bandianxuediao/Breastfeeding_clock/DOC/Photos/1.jpg

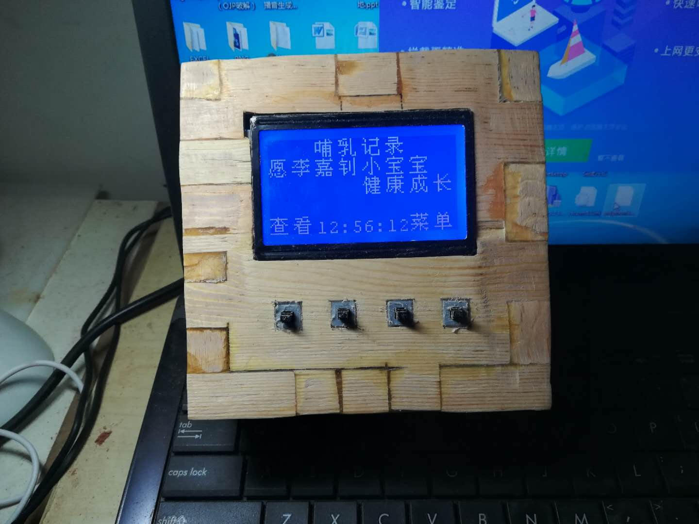
DOC/Photos/1.jpg
