bandianxuediao/Breastfeeding_clock/DOC/Photos/2.jpg

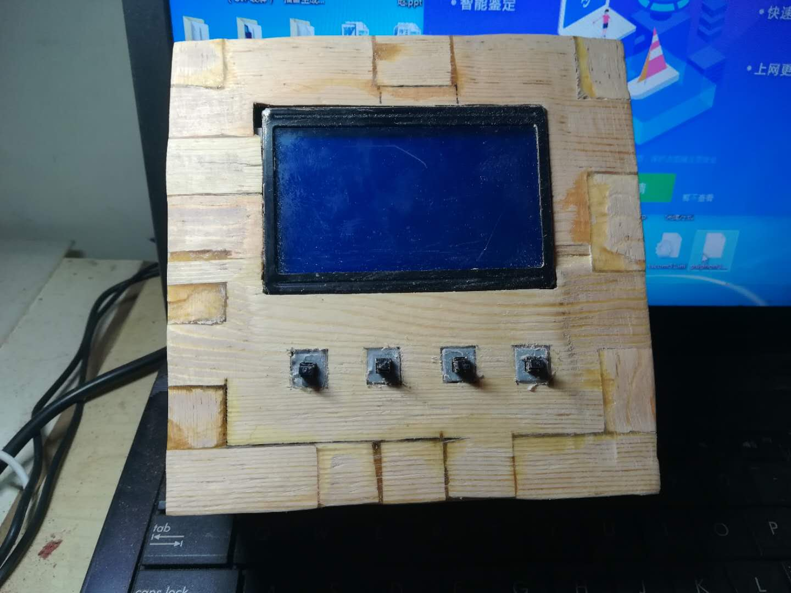
DOC/Photos/2.jpg
