bandianxuediao/Breastfeeding_clock/DOC/Photos/3.jpg

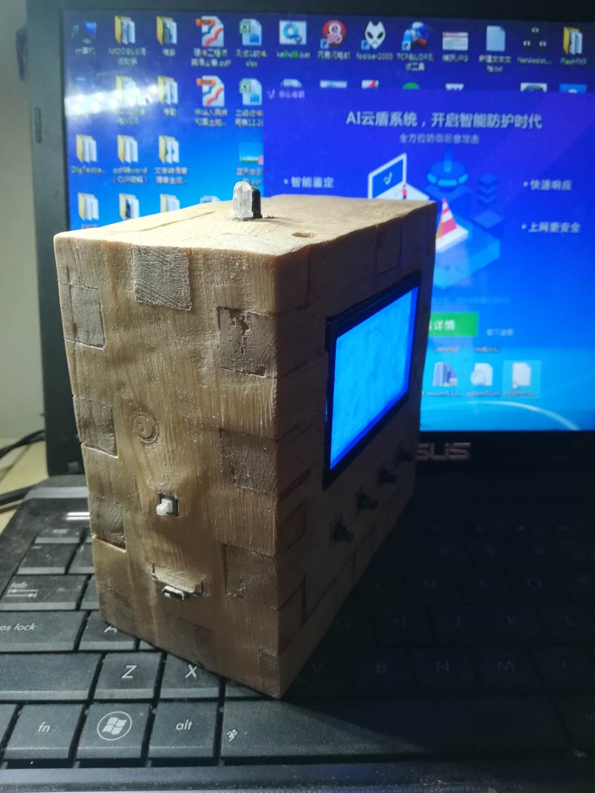
DOC/Photos/3.jpg
