bandianxuediao/Breastfeeding_clock/DOC/Photos/4.jpg

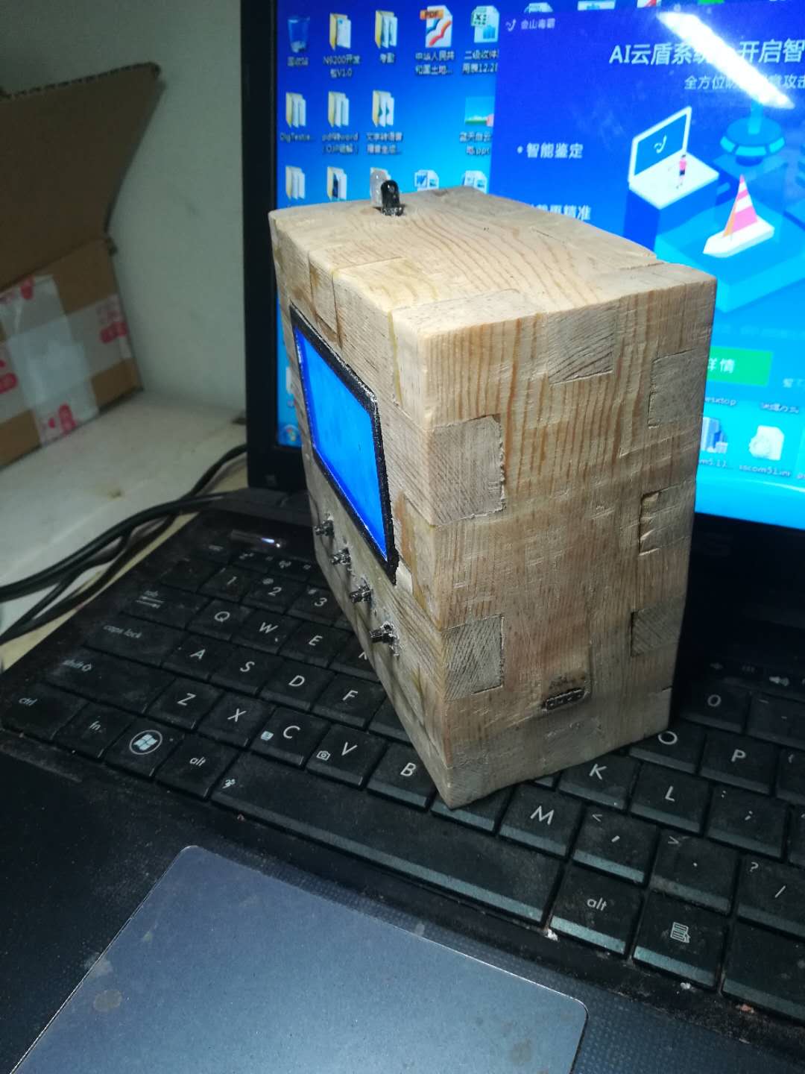
DOC/Photos/4.jpg
