bandianxuediao/Breastfeeding_clock/DOC/Photos/5.jpg

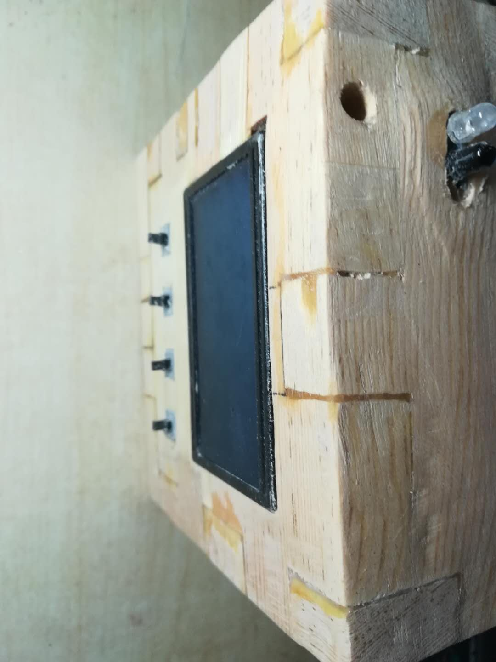
DOC/Photos/5.jpg
