bandianxuediao/Breastfeeding_clock/DOC/Photos/6.jpg

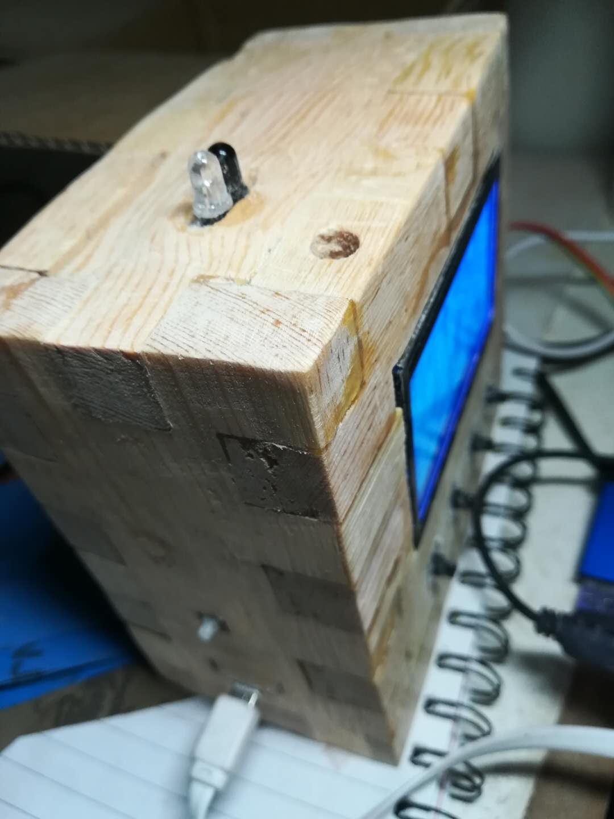
DOC/Photos/6.jpg
