bandianxuediao/Breastfeeding_clock/DOC/Photos/7.jpg

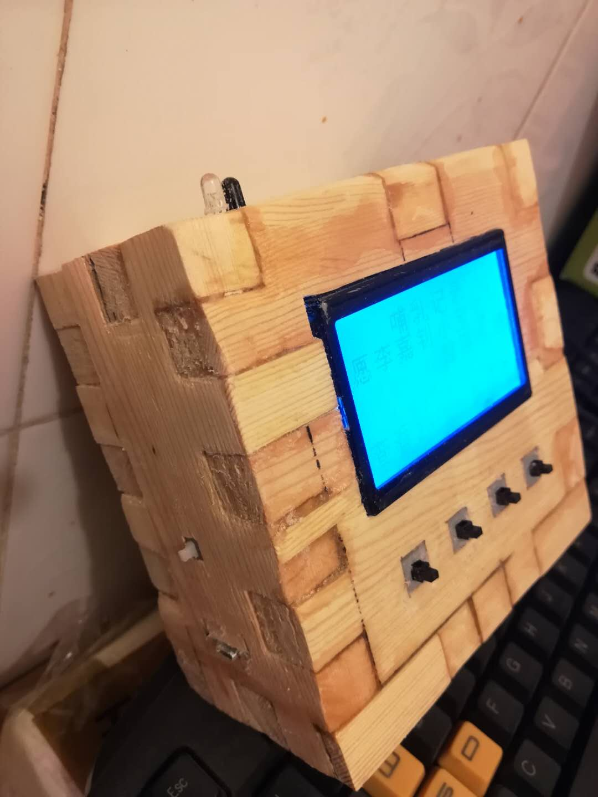
DOC/Photos/7.jpg
