bandianxuediao/Breastfeeding_clock/DOC/Photos/8.jpg

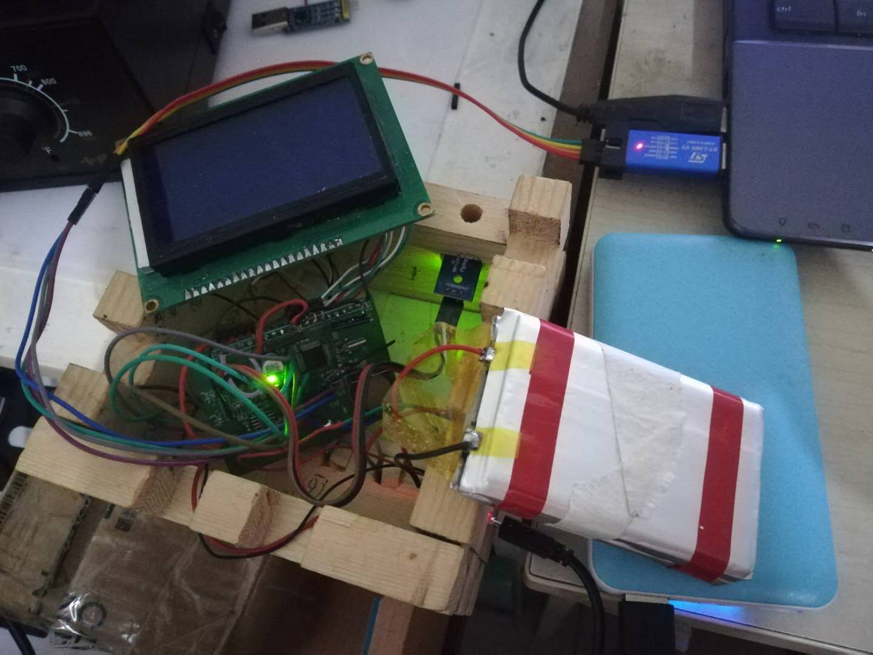
DOC/Photos/8.jpg
