bandianxuediao/Breastfeeding_clock/DOC/Photos/9.jpg

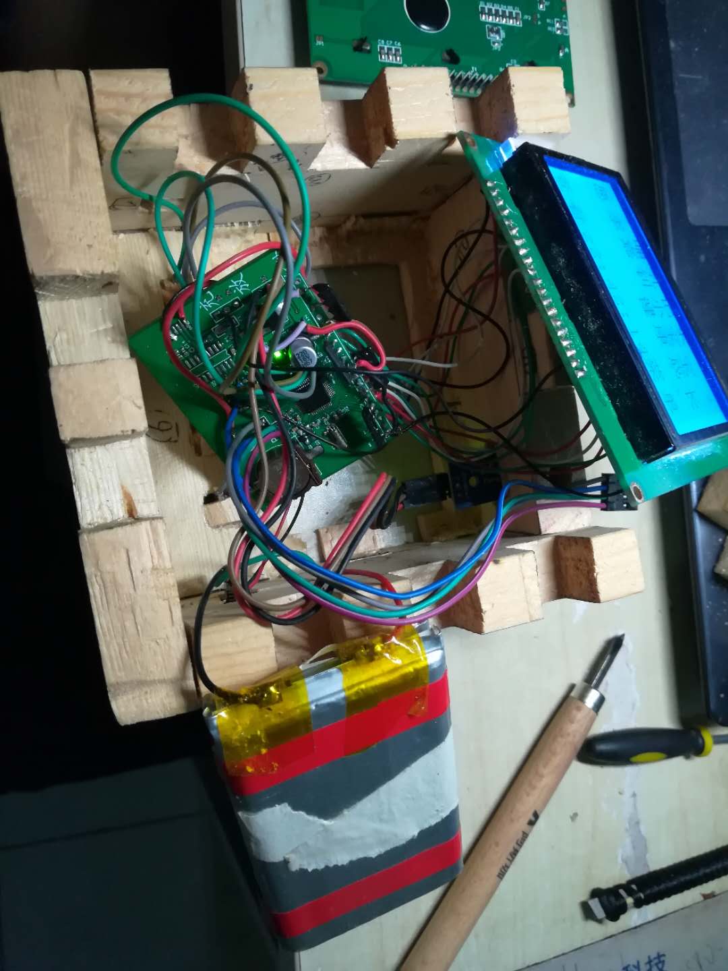
DOC/Photos/9.jpg
