bandianxuediao/Breastfeeding_clock/DOC/Photos/11.jpg

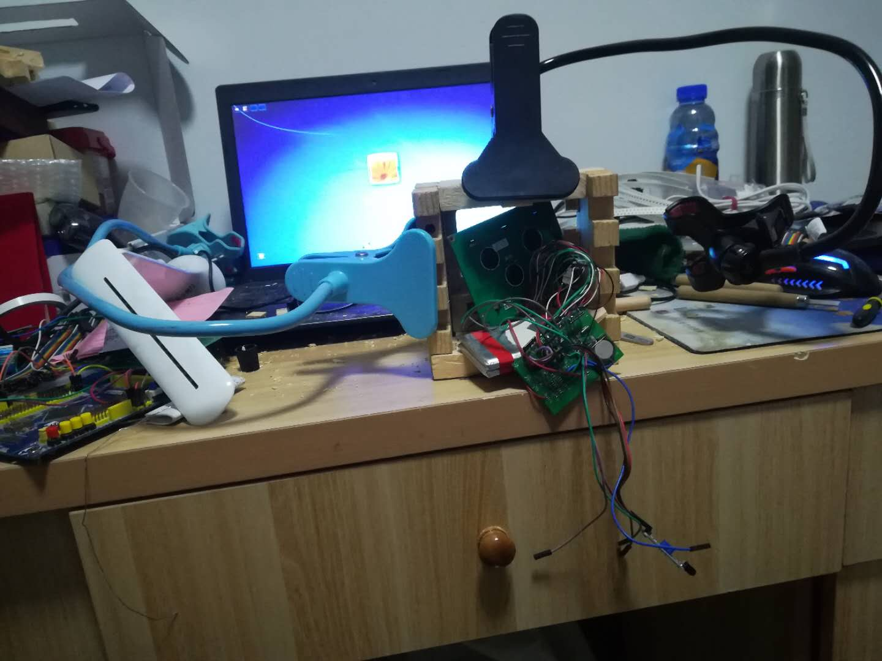
DOC/Photos/11.jpg
