bandianxuediao/Breastfeeding_clock/DOC/Photos/12.jpg

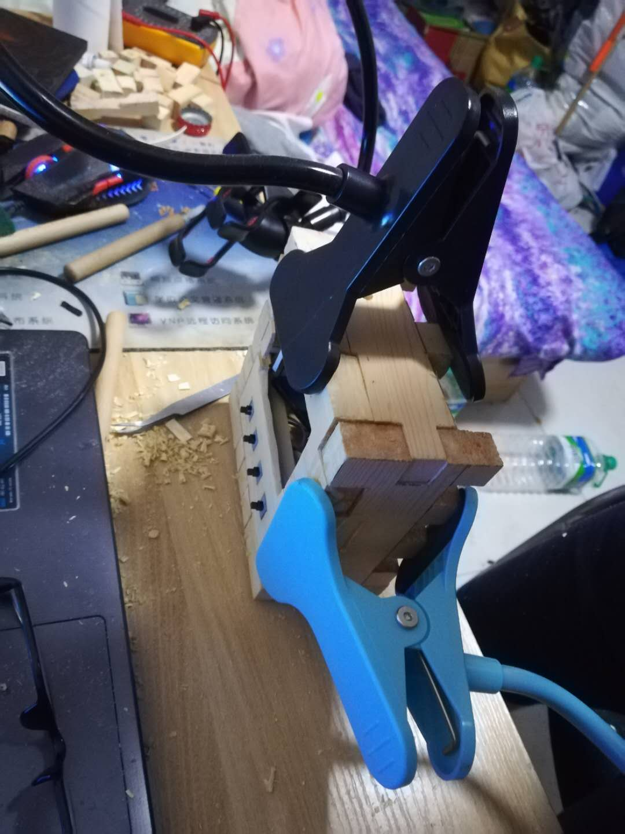
DOC/Photos/12.jpg
