bandianxuediao/Breastfeeding_clock/DOC/Photos/13.jpg

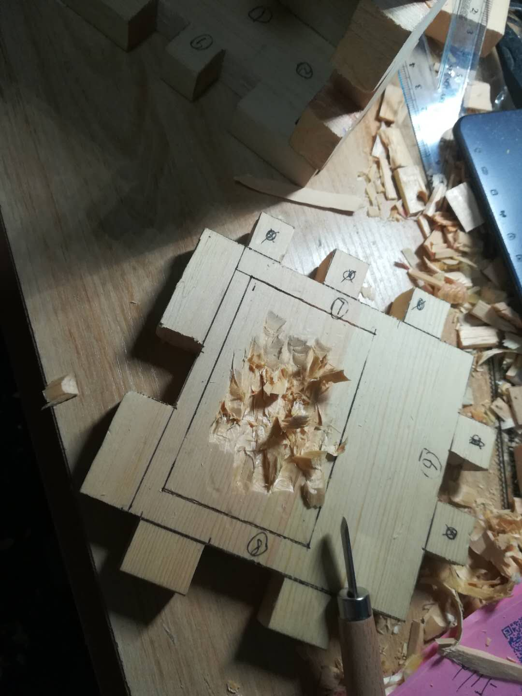
DOC/Photos/13.jpg
