bandianxuediao/Breastfeeding_clock/DOC/Photos/14.jpg

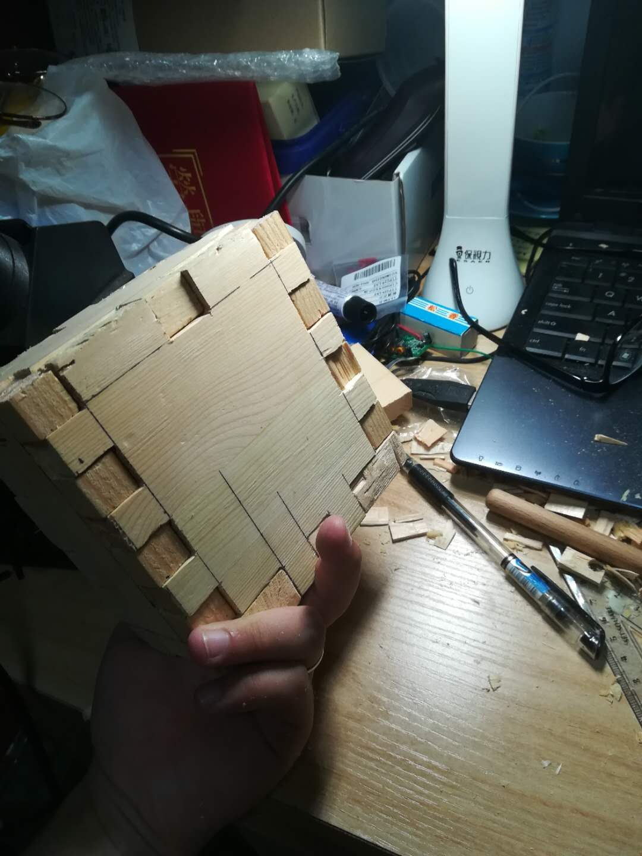
DOC/Photos/14.jpg
