bandianxuediao/Breastfeeding_clock/DOC/Photos/16.jpg

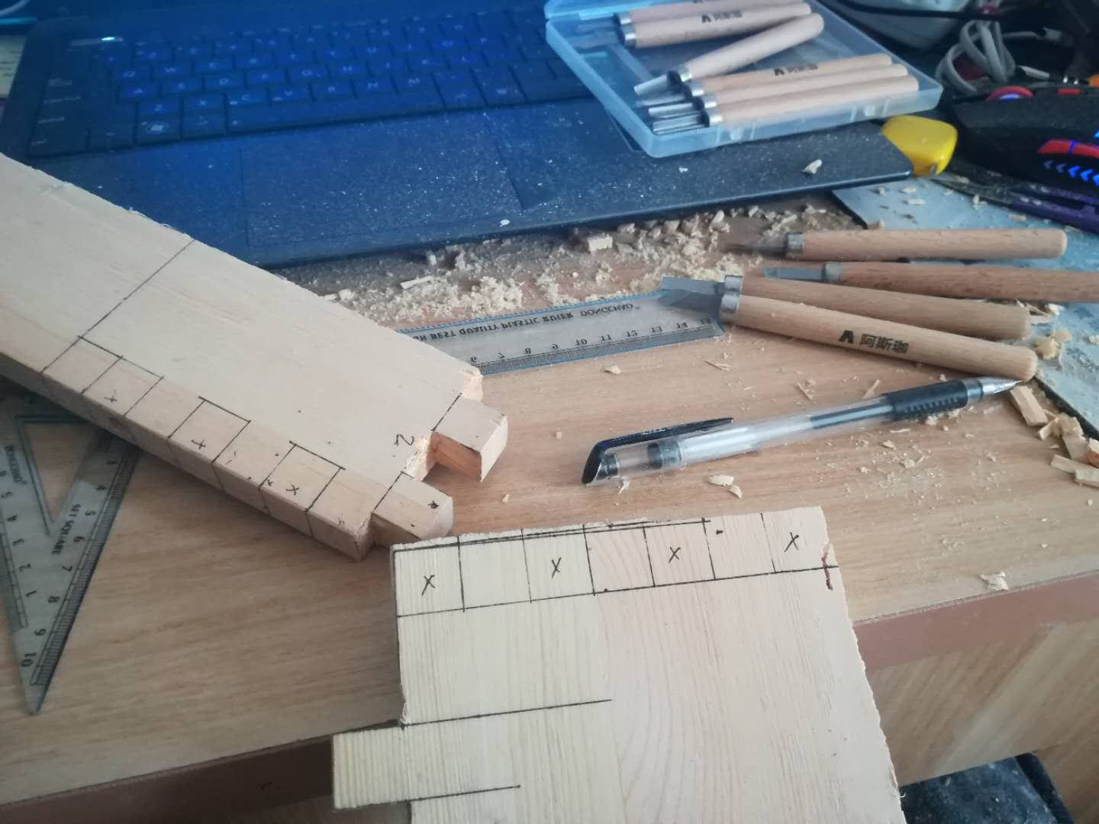
DOC/Photos/16.jpg
