bandianxuediao/Breastfeeding_clock/DOC/Photos/HappyMouse.jpg

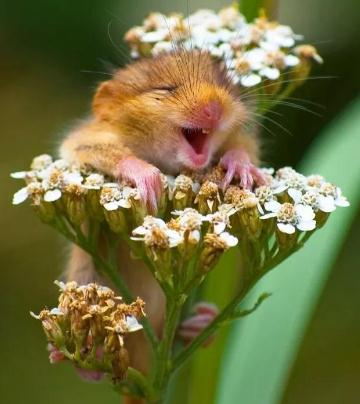
DOC/Photos/HappyMouse.jpg
