bandianxuediao/Breastfeeding_clock/DOC/Photos/soogif.gif

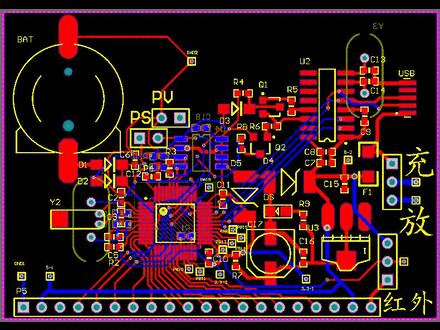
DOC/Photos/soogif.gif
