bandianxuediao/Breastfeeding_clock/Program/HARDWARE/BEEP/beep.h

#ifndef __BEEP_H
#define __BEEP_H
#include "sys.h"
//////////////////////////////////////////////////////////////////////////////////
//本程序只供学习使用，未经作者许可，不得用于其它任何用途

//////////////////////////////////////////////////////////////////////////////////
//蜂鸣器端口定义
#define BEEP PCout(12)  // BEEP,蜂鸣器接口         
#define BL PEout(10)
void BEEP_Init(void);   //初始化

#endif
