bandianxuediao/Breastfeeding_clock/Program/HARDWARE/exti/exti.c

#include "includes.h"


//////////////////////////////////////////////////////////////////////////////////
//本程序只供学习使用，未经作者许可，不得用于其它任何用途
//ALIENTEK精英STM32开发板
//外部中断 驱动代码
//正点原子@ALIENTEK
//技术论坛:www.openedv.com
//修改日期:2012/9/3
//版本：V1.0
//版权所有，盗版必究。
//Copyright(C) 广州市星翼电子科技有限公司 2009-2019
//All rights reserved
//////////////////////////////////////////////////////////////////////////////////

//按键初始化函数
void KEY_Init(void) //IO初始化
{
	GPIO_InitTypeDef GPIO_InitStructure;

	RCC_APB2PeriphClockCmd(RCC_APB2Periph_GPIOB, ENABLE); //使能PORTA,PORTE时钟

	GPIO_InitStructure.GPIO_Pin  = GPIO_Pin_12;//KEY0-KEY1
	GPIO_InitStructure.GPIO_Mode = GPIO_Mode_IN_FLOATING; //设置成下拉输入
	GPIO_Init(GPIOB, &GPIO_InitStructure);//初始化GPIOE4,3


}
//外部中断0服务程序
void EXTIX_Init(void)
{

	EXTI_InitTypeDef EXTI_InitStructure;
	NVIC_InitTypeDef NVIC_InitStructure;

	KEY_Init();  // 按键端口初始化

	RCC_APB2PeriphClockCmd(RCC_APB2Periph_AFIO, ENABLE); //使能复用功能时钟



	//GPIOE.3      中断线以及中断初始化配置 下降沿触发 //KEY1
	GPIO_EXTILineConfig(GPIO_PortSourceGPIOB, GPIO_PinSource12);
	EXTI_InitStructure.EXTI_Line = EXTI_Line12;
	EXTI_InitStructure.EXTI_Mode = EXTI_Mode_Interrupt;
	EXTI_InitStructure.EXTI_Trigger = EXTI_Trigger_Rising_Falling;
	EXTI_Init(&EXTI_InitStructure);     //根据EXTI_InitStruct中指定的参数初始化外设EXTI寄存器


	NVIC_InitStructure.NVIC_IRQChannel = EXTI15_10_IRQn;            //使能按键KEY1所在的外部中断通道
	NVIC_InitStructure.NVIC_IRQChannelPreemptionPriority = 0x02;    //抢占优先级2
	NVIC_InitStructure.NVIC_IRQChannelSubPriority = 0x01;                   //子优先级1
	NVIC_InitStructure.NVIC_IRQChannelCmd = ENABLE;                             //使能外部中断通道
	NVIC_Init(&NVIC_InitStructure);       //根据NVIC_InitStruct中指定的参数初始化外设NVIC寄存器


}




//外部中断3服务程序
void EXTI15_10_IRQHandler(void)
{
	delay_ms(100);//消抖

	if(KEY1 == 0) //按键KEY1
	{
		//PBout(9)=!PBout(9);
	}

	EXTI_ClearITPendingBit(EXTI_Line12);  //清除LINE3上的中断标志位
}
