bandianxuediao/Breastfeeding_clock/Program/User_app/key_right.c

#include "includes.h"

//==================================================================================================
//| 函数名称 | KeyRight_Program
//|----------|--------------------------------------------------------------------------------------
//| 函数功能 | 右键相关流程
//|----------|--------------------------------------------------------------------------------------
//| 输入参数 | 无
//|----------|--------------------------------------------------------------------------------------
//| 返回参数 | 无
//|----------|--------------------------------------------------------------------------------------
//| 函数设计 | 编写人：李亚东    时间：2018-04-21
//|----------|--------------------------------------------------------------------------------------
//|   备注   |
//|----------|--------------------------------------------------------------------------------------
//| 修改记录 | 修改人：          时间：         修改内容：
//==================================================================================================
void KeyRight_Program(void)
{
	switch(Current_state)
	{

		case DISPLAY_ITEM_LACTATION://显示项目状态--默认选中哺乳
		case DISPLAY_ITEM_DRINK://显示项目状态--选中补水
		case DISPLAY_ITEM_SHIT://显示项目状态--选中大便
		case DISPLAY_ITEM_URINATE://显示项目状态--选中小便
		case DISPLAY_MENU_TIME:
		case DISPLAY_MENU_CLEAR_WAIT:
			ShowWelcome();
			Current_state = WELCOME_WAIT;
			break;

		case MODIFY_YEAR://修改当前年
		case MODIFY_MONTH://修改月
		case MODIFY_DATE://修改日
		case MODIFY_HOUR://修改小时
		case MODIFY_MIN://修改分钟
		case MODIFY_SEC://修改秒



		case        SELECT_YEAR://选中年
		case    SELECT_MONTH://选中月
		case    SELECT_DATE://选中日
		case    SELECT_HOUR://选中小时
		case    SELECT_MIN://选中分钟
		case    SELECT_SEC://选中秒
		case DISPLAY_CURRENT_TIME:
		case WELCOME_WAIT:
			Display_Menu(1);
			Current_state = DISPLAY_MENU_TIME;
			break;

		case LACTATION_LIST:
			Display_Items(1);   //默认为选中Lactation
			Current_state = DISPLAY_ITEM_LACTATION; //当前状态置为项目显示
			break;

		case DRINK_LIST:
			Display_Items(3);   //默认为选中Lactation
			Current_state = DISPLAY_ITEM_DRINK; //当前状态置为项目显示
			break;

		case SHIT_LIST:
			Display_Items(2);   //默认为选中Lactation
			Current_state = DISPLAY_ITEM_SHIT; //当前状态置为项目显示
			break;

		case URINATE_LIST:
			Display_Items(4);   //默认为选中Lactation
			Current_state = DISPLAY_ITEM_URINATE; //当前状态置为项目显示
			break;



		default:
			break;

	}
}
