bandianxuediao/Breastfeeding_clock/Program/HARDWARE/EEPROM/EE_IIC.c

#include "includes.h"
//////////////////////////////////////////////////////////////////////////////////
//本程序只供学习使用，未经作者许可，不得用于其它任何用途
//ALIENTEK精英STM32开发板
//IIC驱动 代码
//正点原子@ALIENTEK
//技术论坛:www.openedv.com
//修改日期:2012/9/9
//版本：V1.0
//版权所有，盗版必究。
//Copyright(C) 广州市星翼电子科技有限公司 2009-2019
//All rights reserved
//////////////////////////////////////////////////////////////////////////////////

//初始化IIC
void EE_IIC_Init(void)
{
	GPIO_InitTypeDef GPIO_InitStructure;
	RCC_APB2PeriphClockCmd( RCC_APB2Periph_GPIOB, ENABLE ); //使能GPIOB时钟
	GPIO_InitStructure.GPIO_Pin = GPIO_Pin_6 | GPIO_Pin_7;
	GPIO_InitStructure.GPIO_Mode = GPIO_Mode_Out_PP ;   //推挽输出
	GPIO_InitStructure.GPIO_Speed = GPIO_Speed_50MHz;
	GPIO_Init(GPIOB, &GPIO_InitStructure);
	GPIO_SetBits(GPIOB, GPIO_Pin_6 | GPIO_Pin_7); //PB10,PB11 输出高电平

	if(AT24CXX_ReadOneByte(INITIAL_ADDR) != 0x55) //判断是不是第一次启动，第一次启动将索引区清零
	{
		AT24CXX_WriteOneByte(INITIAL_ADDR, 0x55);
		//AT24CXX_WriteLenByte(6, 1801010620, 4);

		AT24CXX_WriteLenByte(10, 0, 2);
		AT24CXX_WriteLenByte(20, 0, 2);
		AT24CXX_WriteLenByte(30, 0, 2);
		AT24CXX_WriteLenByte(40, 0, 2);
	}

}
//产生IIC起始信号
void EE_IIC_Start(void)
{
	EE_SDA_OUT();     //sda线输出
	EE_IIC_SDA = 1;
	EE_IIC_SCL = 1;
	delay_us(4);
	EE_IIC_SDA = 0; //START:when CLK is high,DATA change form high to low
	delay_us(4);
	EE_IIC_SCL = 0; //钳住I2C总线，准备发送或接收数据
}
//产生IIC停止信号
void EE_IIC_Stop(void)
{
	EE_SDA_OUT();//sda线输出
	EE_IIC_SCL = 0;
	EE_IIC_SDA = 0; //STOP:when CLK is high DATA change form low to high
	delay_us(4);
	EE_IIC_SCL = 1;
	EE_IIC_SDA = 1; //发送I2C总线结束信号
	delay_us(4);
}
//等待应答信号到来
//返回值：1，接收应答失败
//        0，接收应答成功
u8 EE_IIC_Wait_Ack(void)
{
	u8 ucErrTime = 0;
	EE_SDA_IN();      //SDA设置为输入
	EE_IIC_SDA = 1;
	delay_us(1);
	EE_IIC_SCL = 1;
	delay_us(1);

	while(EE_READ_SDA)
	{
		ucErrTime++;

		if(ucErrTime > 250)
		{
			EE_IIC_Stop();
			return 1;
		}
	}

	EE_IIC_SCL = 0; //时钟输出0
	return 0;
}
//产生ACK应答
void EE_IIC_Ack(void)
{
	EE_IIC_SCL = 0;
	EE_SDA_OUT();
	EE_IIC_SDA = 0;
	delay_us(2);
	EE_IIC_SCL = 1;
	delay_us(2);
	EE_IIC_SCL = 0;
}
//不产生ACK应答
void EE_IIC_NAck(void)
{
	EE_IIC_SCL = 0;
	EE_SDA_OUT();
	EE_IIC_SDA = 1;
	delay_us(2);
	EE_IIC_SCL = 1;
	delay_us(2);
	EE_IIC_SCL = 0;
}
//IIC发送一个字节
//返回从机有无应答
//1，有应答
//0，无应答
void EE_IIC_Send_Byte(u8 txd)
{
	u8 t;
	EE_SDA_OUT();
	EE_IIC_SCL = 0; //拉低时钟开始数据传输

	for(t = 0; t < 8; t++)
	{
		EE_IIC_SDA = (txd & 0x80) >> 7;
		txd <<= 1;
		delay_us(2);   //对TEA5767这三个延时都是必须的
		EE_IIC_SCL = 1;
		delay_us(2);
		EE_IIC_SCL = 0;
		delay_us(2);
	}
}
//读1个字节，ack=1时，发送ACK，ack=0，发送nACK
u8 EE_IIC_Read_Byte(unsigned char ack)
{
	unsigned char i, receive = 0;
	EE_SDA_IN();//SDA设置为输入

	for(i = 0; i < 8; i++ )
	{
		EE_IIC_SCL = 0;
		delay_us(2);
		EE_IIC_SCL = 1;
		receive <<= 1;

		if(EE_READ_SDA)receive++;

		delay_us(1);
	}

	if (!ack)
		EE_IIC_NAck();//发送nACK
	else
		EE_IIC_Ack(); //发送ACK

	return receive;
}
